lesterwilliam/qeMotion/3D/Controller/Buttons 1.JPG

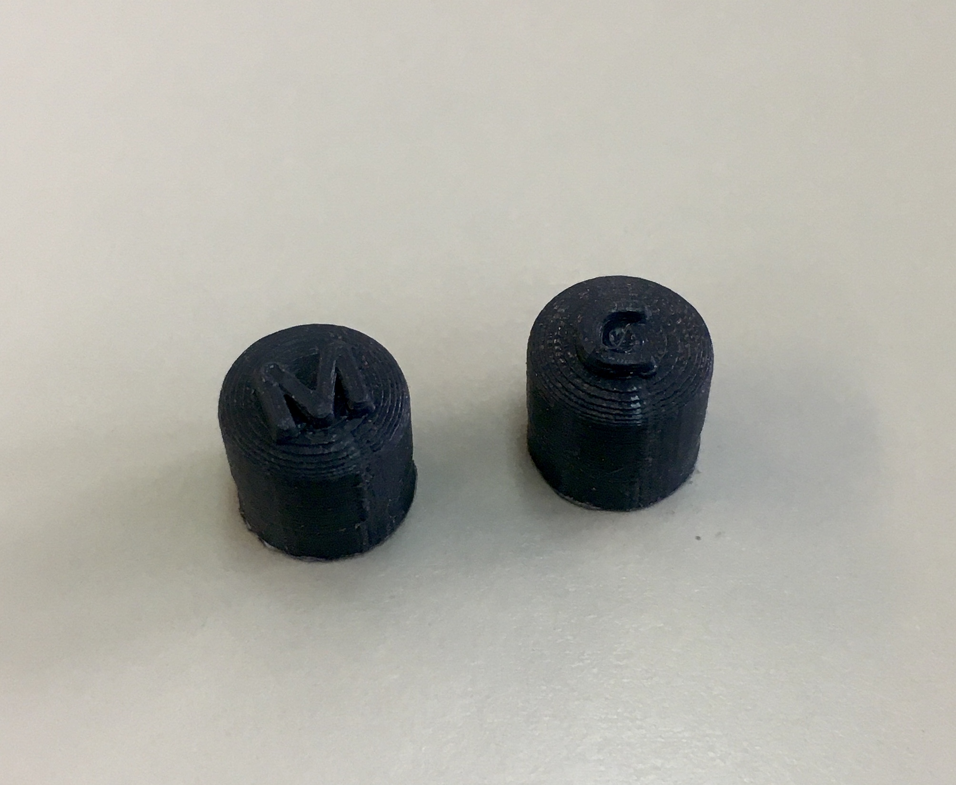
3D/Controller/Buttons 1.JPG
