lesterwilliam/qeMotion/3D/Controller/Buttons 2.JPG

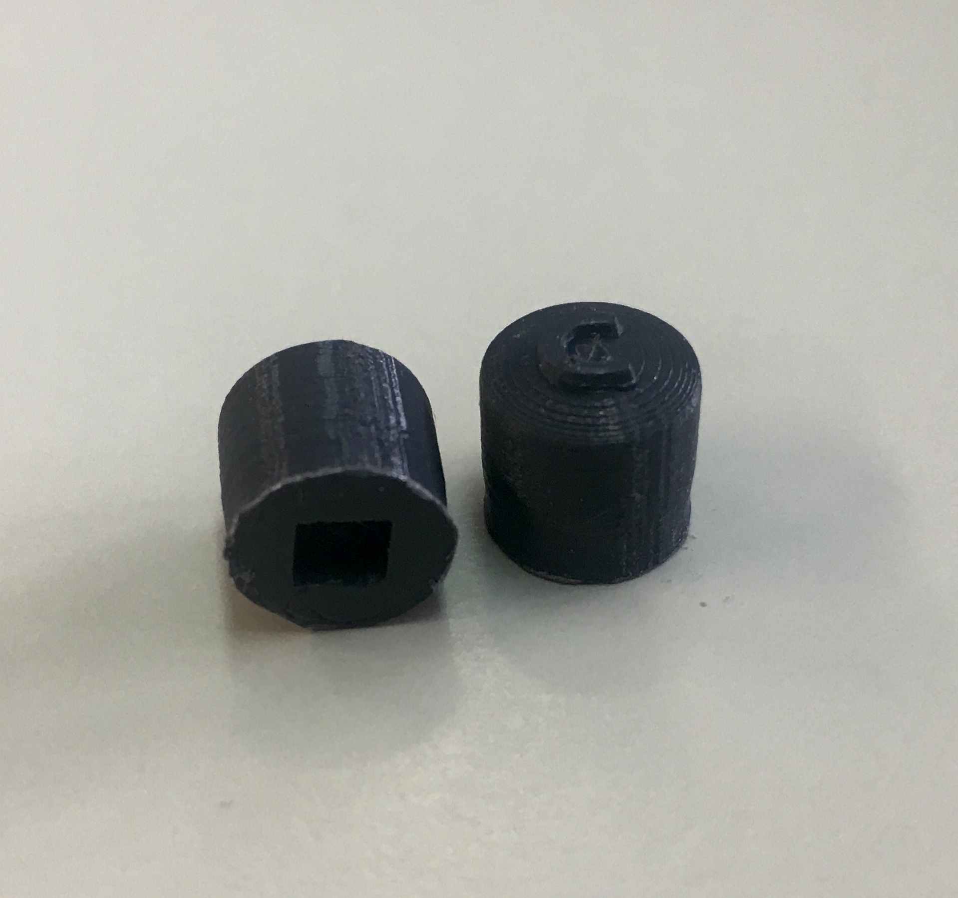
3D/Controller/Buttons 2.JPG
