lesterwilliam/qeMotion/3D/Controller/Buttons 3.JPG

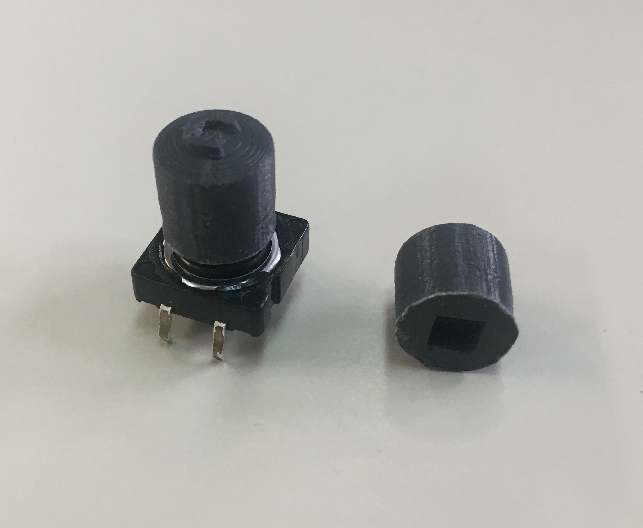
3D/Controller/Buttons 3.JPG
