lesterwilliam/qeMotion/3D/Controller/qeMotion complete 1.JPG

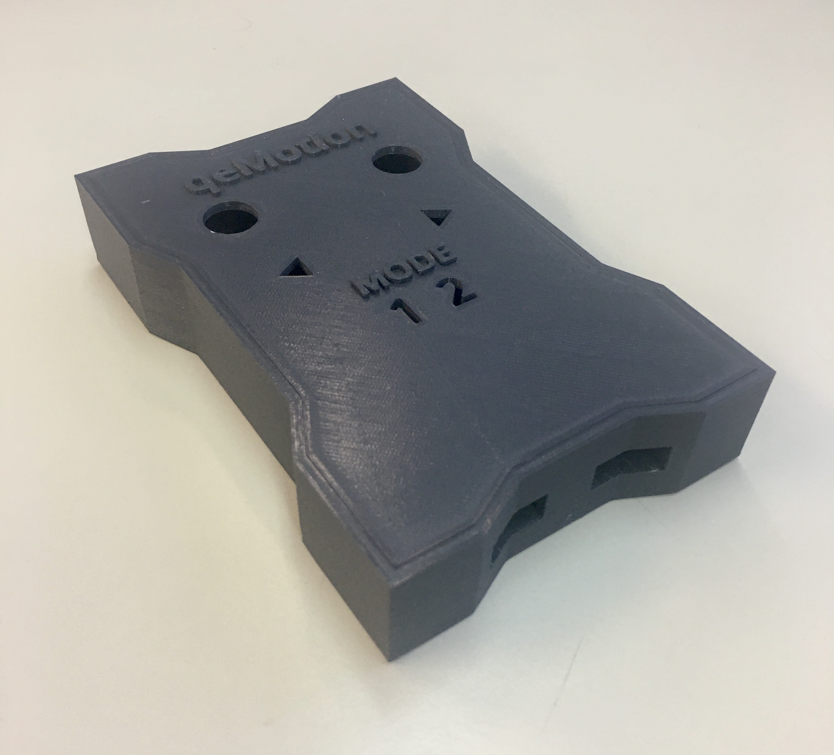
3D/Controller/qeMotion complete 1.JPG
