lesterwilliam/qeMotion/3D/Controller/qeMotion complete 2.JPG

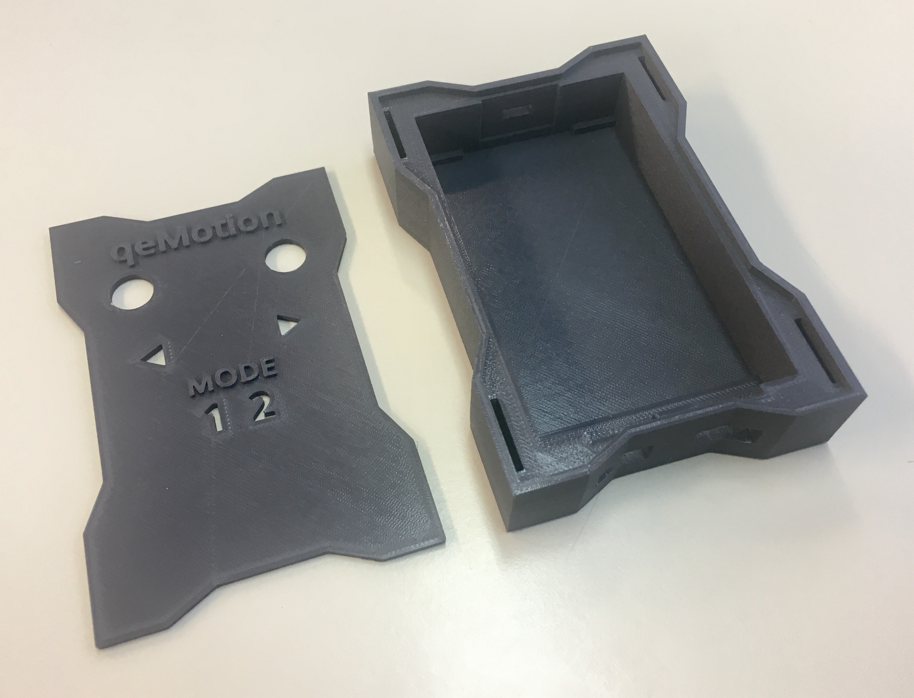
3D/Controller/qeMotion complete 2.JPG
