lesterwilliam/qeMotion/3D/Controller/qeMotion complete render.PNG

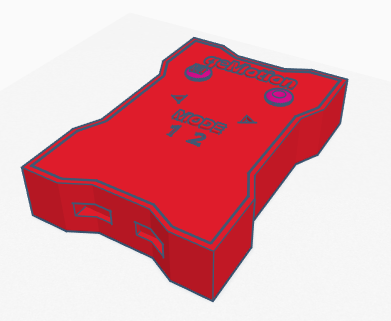
3D/Controller/qeMotion complete render.PNG
