lesterwilliam/qeMotion/3D/Controller/qeMotion lower.JPG

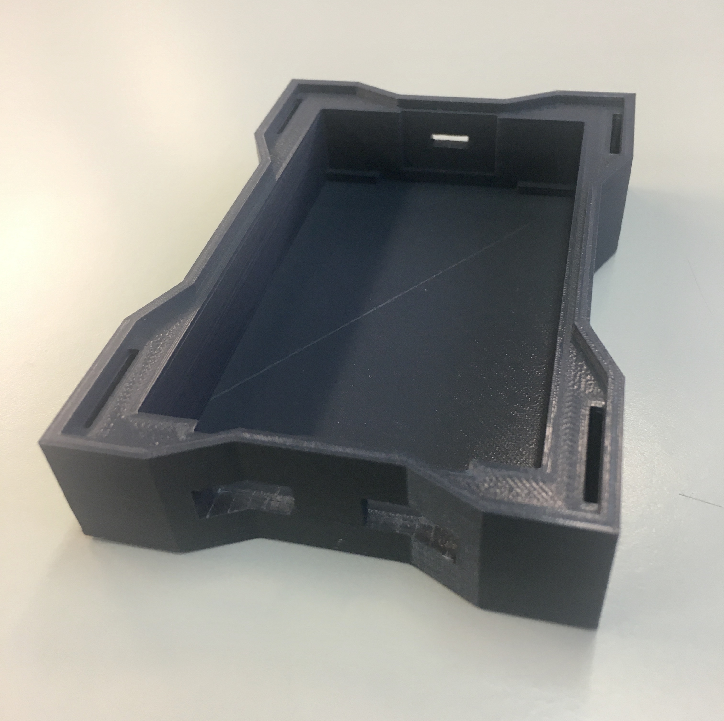
3D/Controller/qeMotion lower.JPG
