lesterwilliam/qeMotion/3D/Controller/qeMotion upper 1.JPG

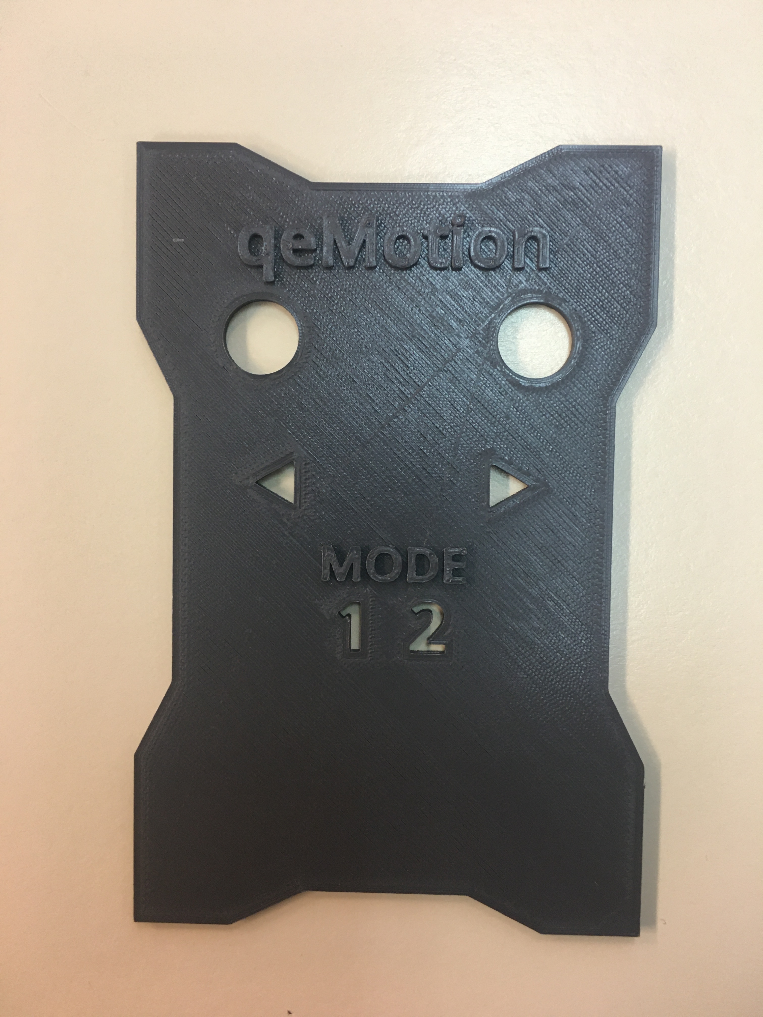
3D/Controller/qeMotion upper 1.JPG
