lesterwilliam/qeMotion/3D/Controller/qeMotion upper 2.JPG

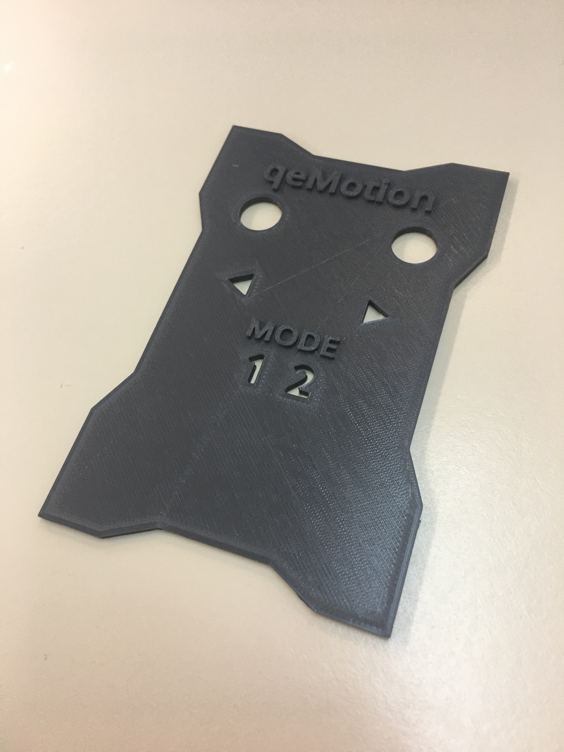
3D/Controller/qeMotion upper 2.JPG
