lesterwilliam/qeMotion/media/Complete/qeMotion complete open 1.JPG

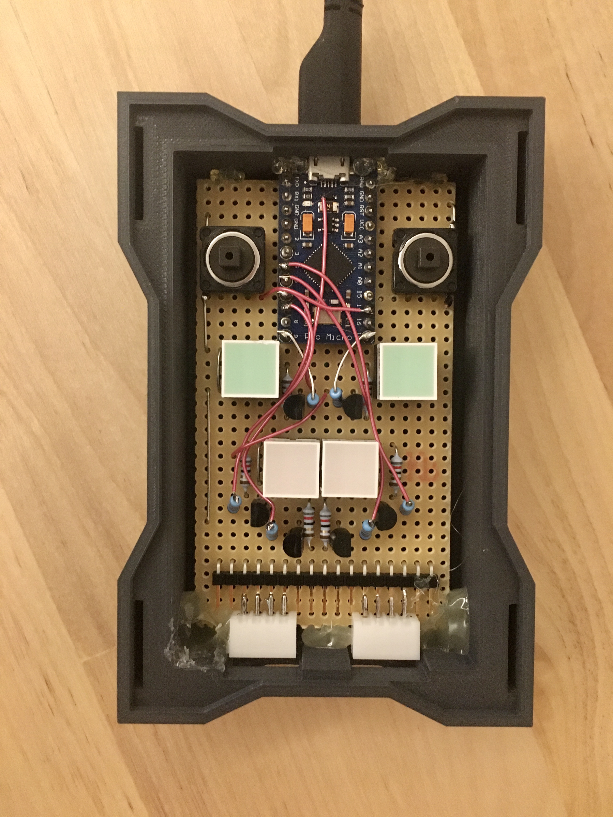
media/Complete/qeMotion complete open 1.JPG
