lesterwilliam/qeMotion/media/Complete/qeMotion complete open 2.JPG

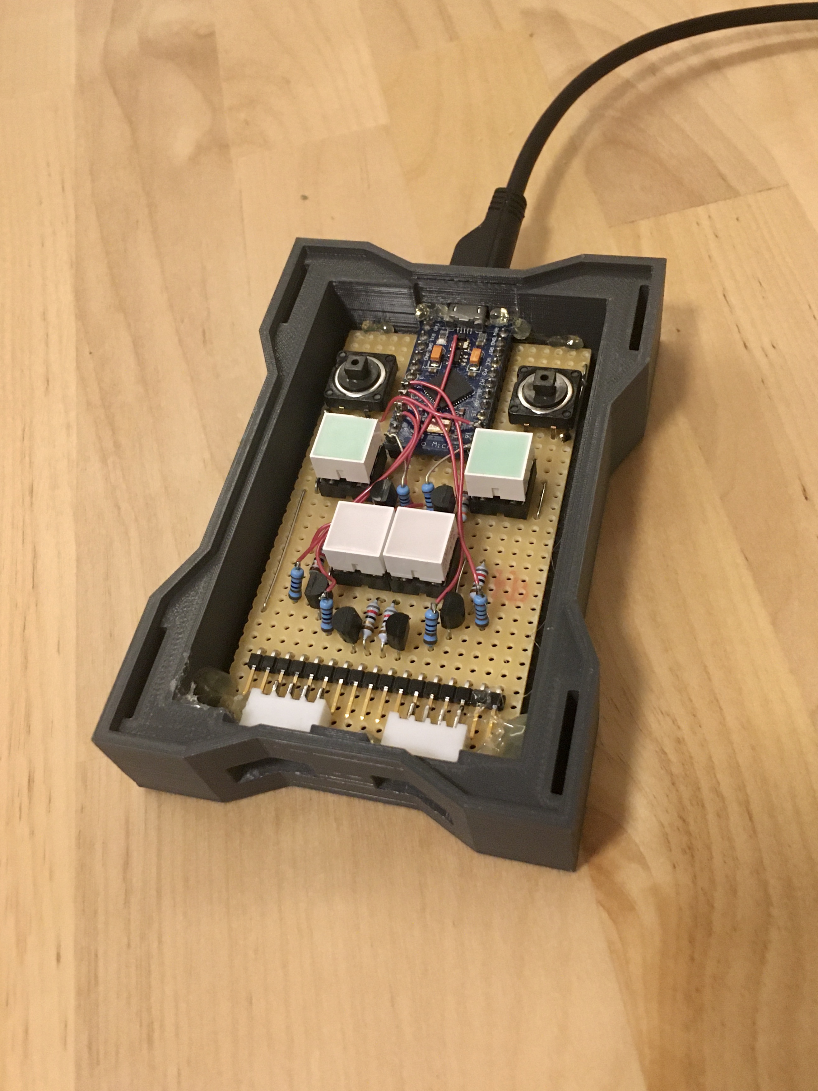
media/Complete/qeMotion complete open 2.JPG
