lesterwilliam/qeMotion/media/Complete/qeMotion complete open 3.JPG

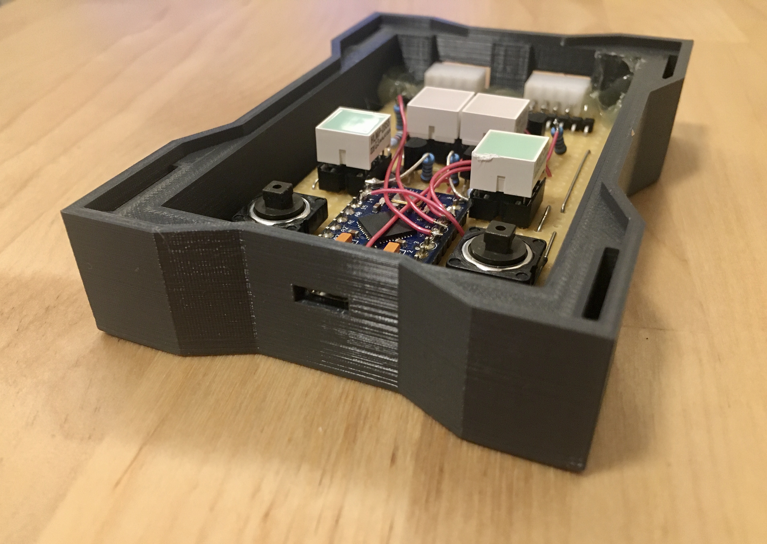
media/Complete/qeMotion complete open 3.JPG
