lesterwilliam/qeMotion/media/Complete/qeMotion with HyperX Addon 1.JPG

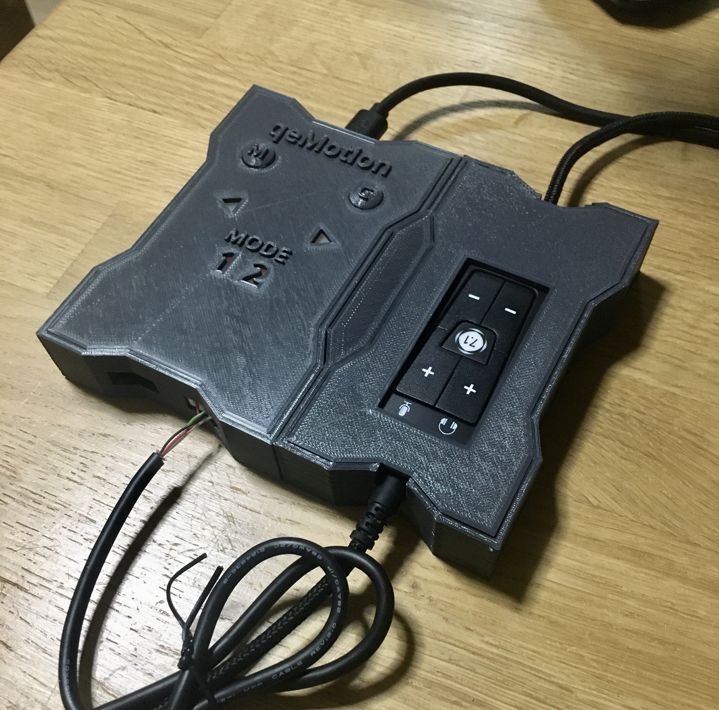
media/Complete/qeMotion with HyperX Addon 1.JPG
