lesterwilliam/qeMotion/media/Complete/qeMotion with HyperX Addon 2.JPG

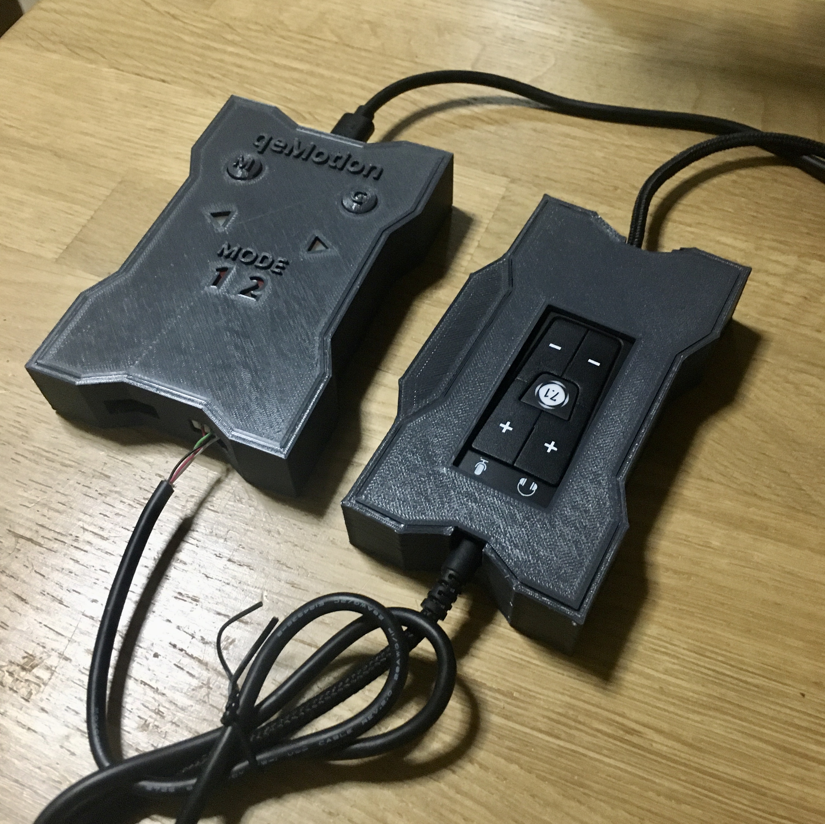
media/Complete/qeMotion with HyperX Addon 2.JPG
