lesterwilliam/qeMotion/media/Complete/qeMotion with HyperX Addon 3.JPG

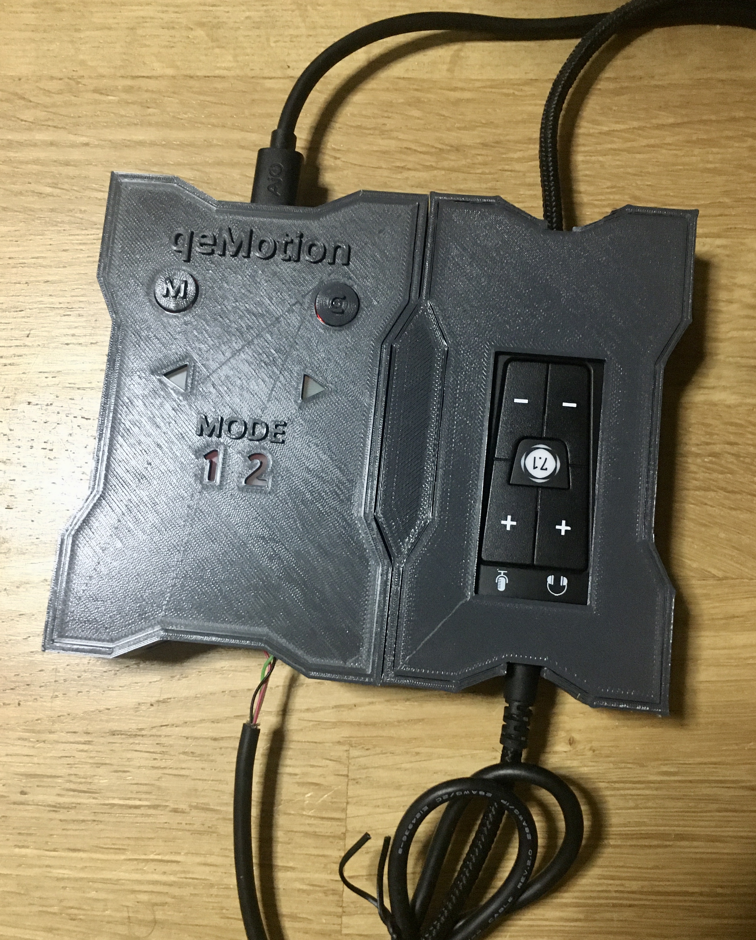
media/Complete/qeMotion with HyperX Addon 3.JPG
