lesterwilliam/qeMotion/media/PCB/PCB front.JPG

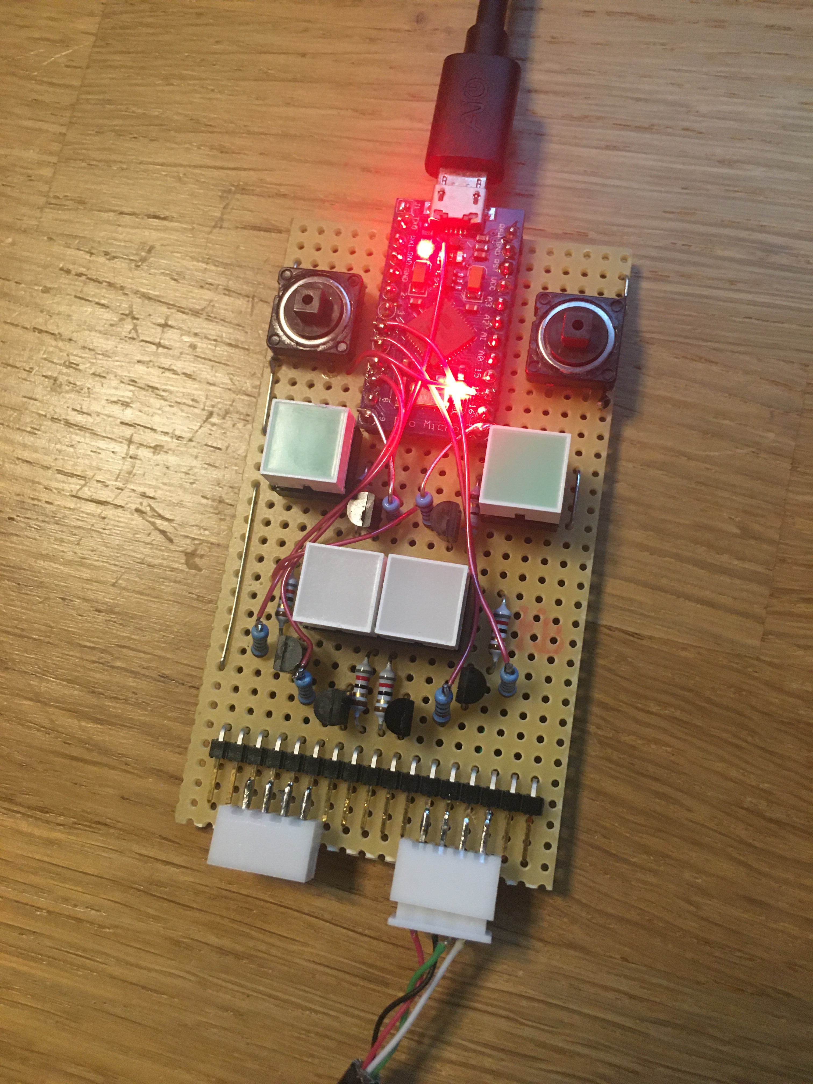
media/PCB/PCB front.JPG
